diabolo38/EdkLight/doc/IMG_20260105_194856.jpg

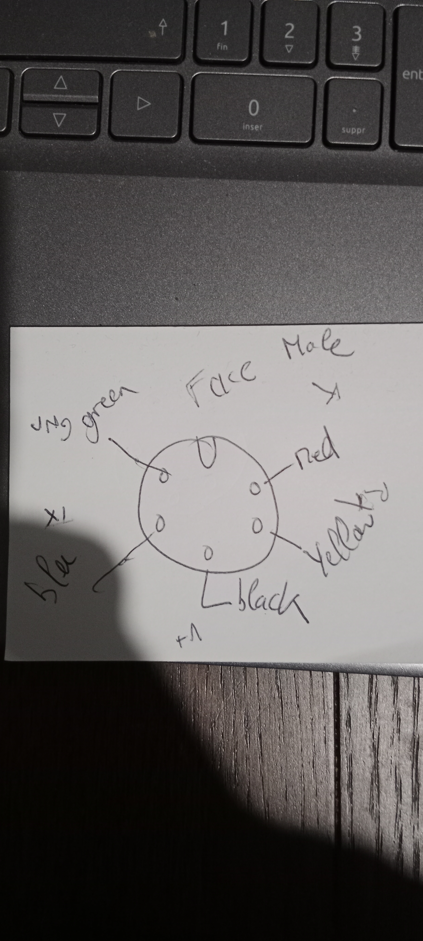
doc/IMG_20260105_194856.jpg
